CedarGroveStudios/PCB_ItsyBitsy_Breadboard_Adapter/photos and graphics/IMG_1394.jpeg

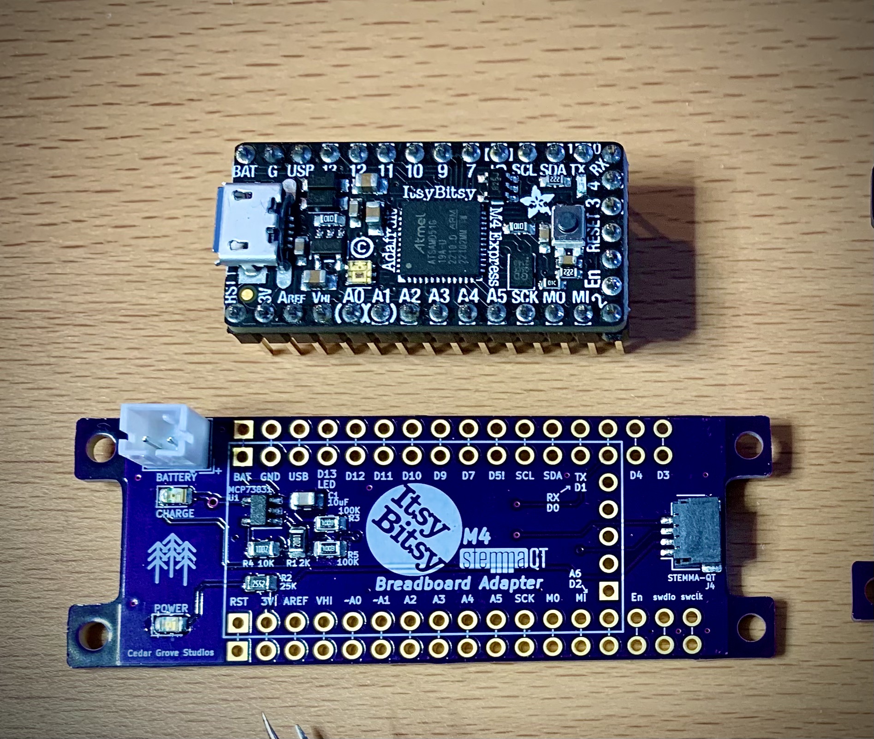
photos and graphics/IMG_1394.jpeg
