CedarGroveStudios/PCB_ItsyBitsy_Breadboard_Adapter/photos and graphics/PCB_glam.png

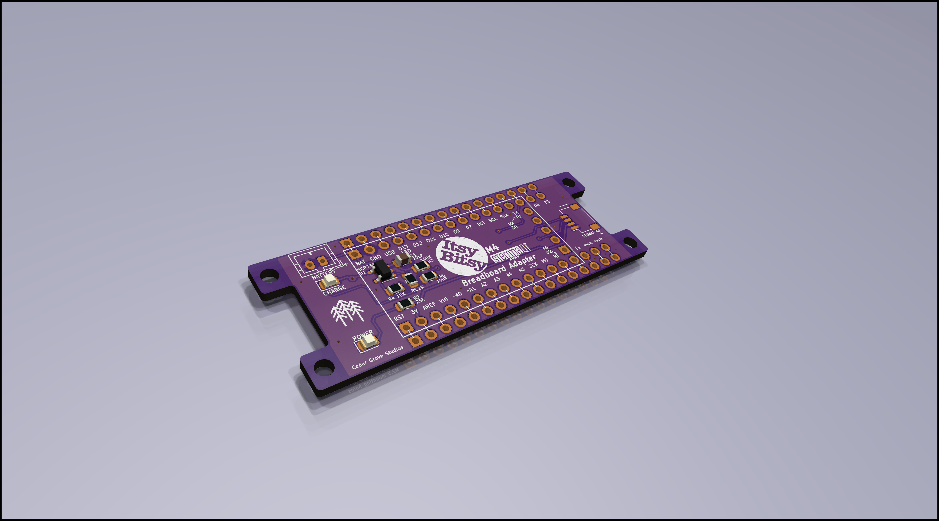
photos and graphics/PCB_glam.png
