CedarGroveStudios/PCB_ItsyBitsy_Breadboard_Adapter/photos and graphics/PCB_stack.png

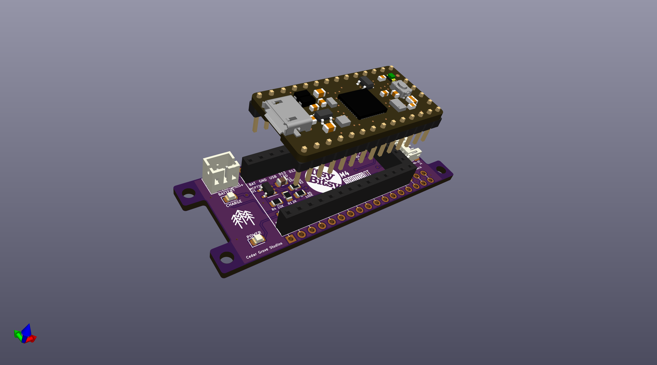
photos and graphics/PCB_stack.png
